sxwid/storyphone_attiny/Märchentelefon.kicad_sch

## KiCad design Märchentelefon.kicad_sch (2023-01-18)

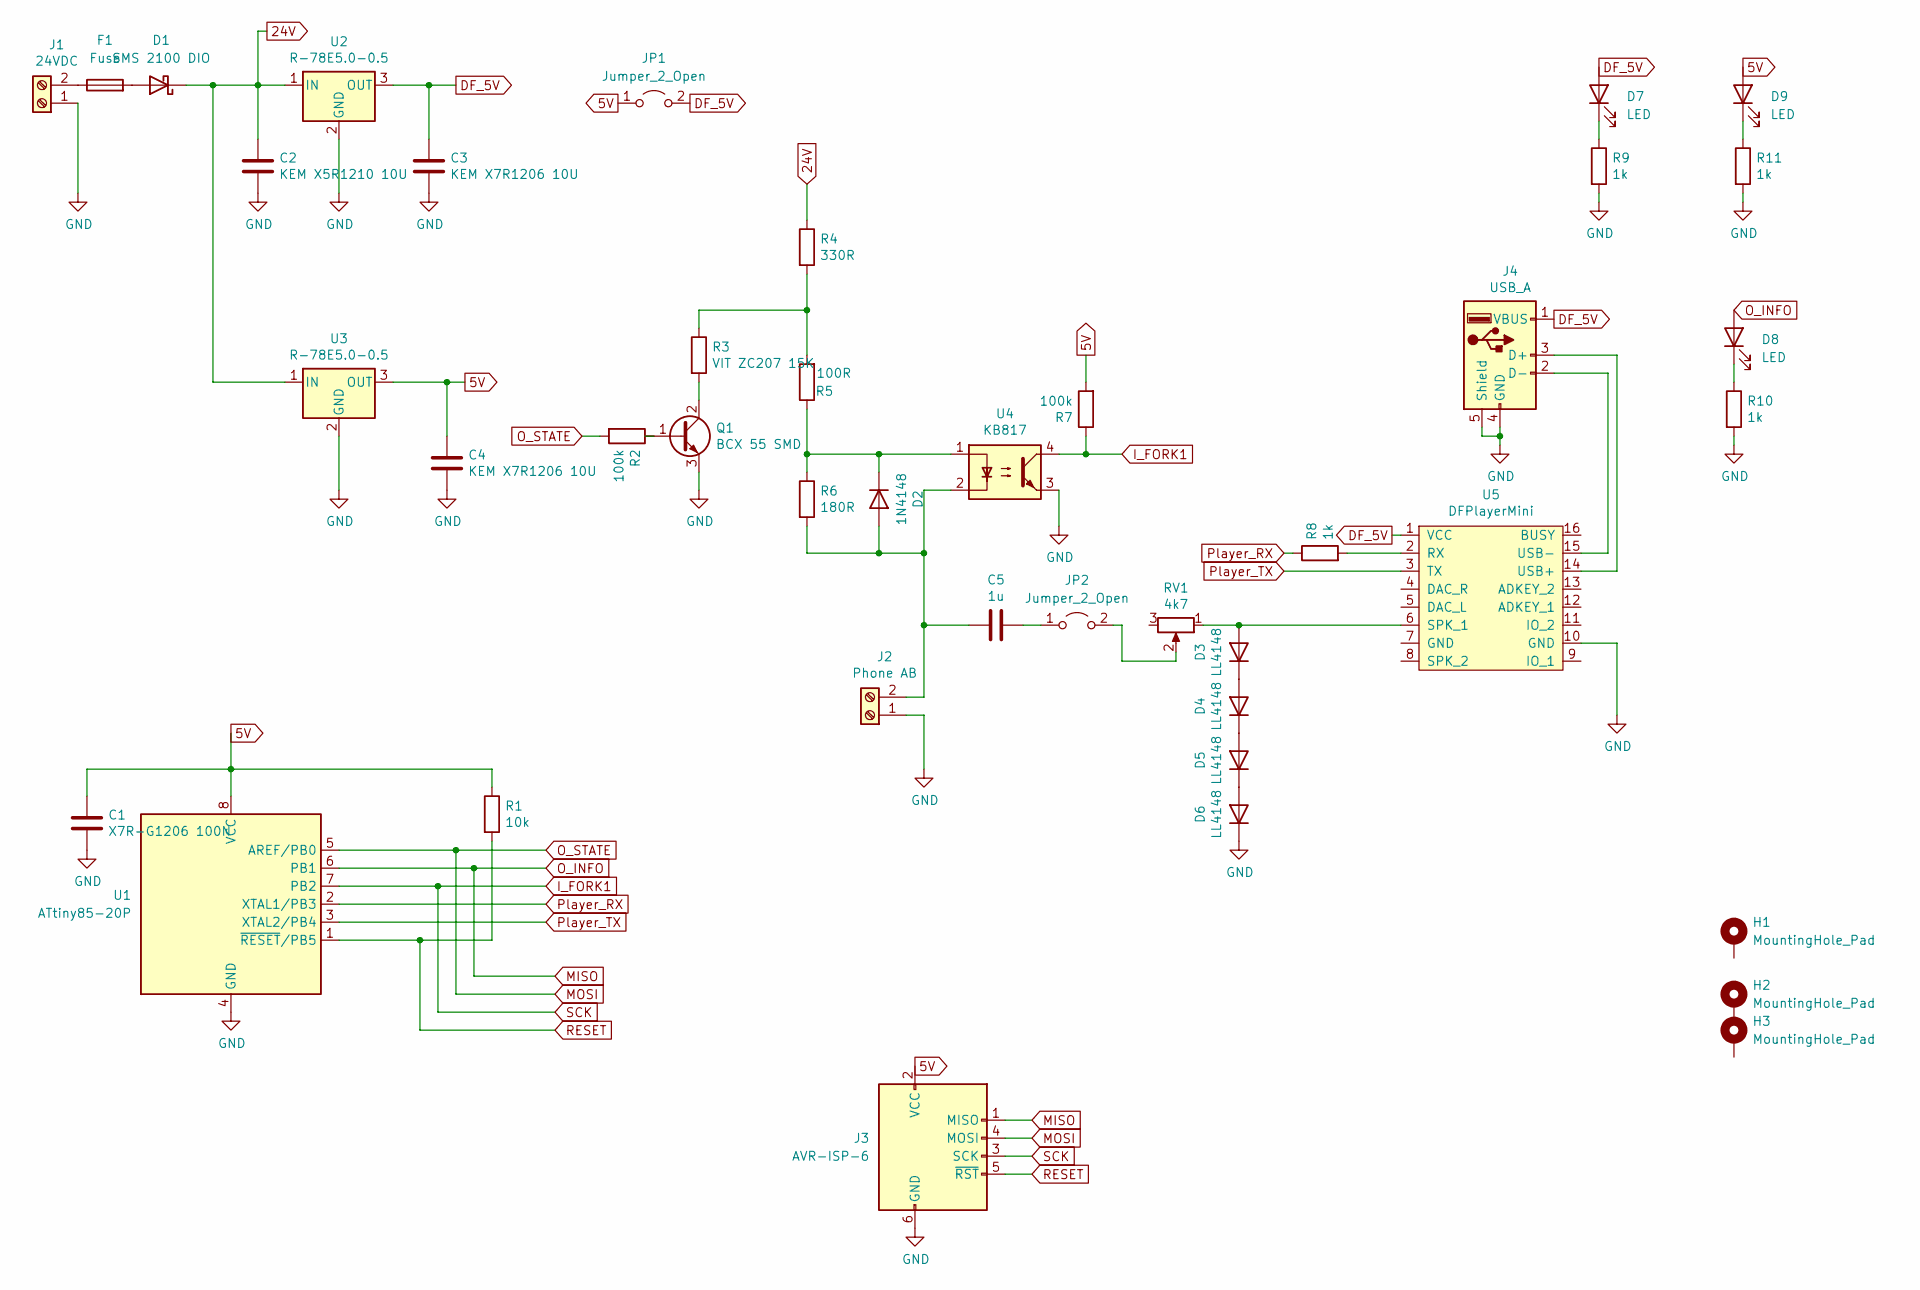
[picture p2: schematic Märchentelefon.kicad_sch]

Parts:
C1: X7R-G1206 100N; C_1206_3216Metric
C2: KEM X5R1210 10U; C_1210_3225Metric
C3, C4: KEM X7R1206 10U; C_1206_3216Metric
C5: 1u; C_Rect_L4.6mm_W5.5mm_P2.50mm_MKS02_FKP02
D1: SMS 2100 DIO; D_MELF_Handsoldering
D2: 1N4148; D_MiniMELF_Handsoldering
D3, D4, D5, D6: LL4148; D_MiniMELF_Handsoldering
D7, D8, D9: LED; LED_0805_2012Metric_Pad1.15x1.40mm_HandSolder
F1: Fuse; Fuse_2512_6332Metric_Pad1.52x3.35mm_HandSolder
H1, H2, H3: MountingHole_Pad; MountingHole_2.5mm
J1: 24VDC; PinSocket_1x02_P2.54mm_Vertical
J2: Phone AB; PinSocket_1x02_P2.54mm_Vertical
J3: AVR-ISP-6
J4: USB_A; USB_A_Molex_67643_Horizontal
JP1, JP2: Jumper_2_Open; L_0805_2012Metric_Pad1.15x1.40mm_HandSolder
Q1: BCX 55 SMD; SOT-89-3_Handsoldering
R1: 10k; R_0805_2012Metric_Pad1.20x1.40mm_HandSolder
R2, R7: 100k; R_0805_2012Metric_Pad1.20x1.40mm_HandSolder
R3: VIT ZC207 15K; R_MELF_MMB-0207
R4: 330R; R_0805_2012Metric_Pad1.20x1.40mm_HandSolder
R5: 100R; R_0805_2012Metric_Pad1.20x1.40mm_HandSolder
R6: 180R; R_0805_2012Metric_Pad1.20x1.40mm_HandSolder
R8, R9, R10, R11: 1k; R_0805_2012Metric_Pad1.20x1.40mm_HandSolder
RV1: 4k7; Potentiometer_Piher_T-16H_Single_Horizontal
U1: ATtiny85-20P; DIP-8_W7.62mm
U2, U3: R-78E5.0-0.5; Converter_DCDC_RECOM_R-78E-0.5_THT
U4: KB817; DIP-4_W7.62mm
U5: DFPlayerMini; DFPlayer_V2

Connections:
5V: C1.1, C4.1, D9.2 (A), J3.2 (VCC), JP1.1 (A), R1.1, R7.2, U1.8 (VCC), U3.3 (OUT)
24V: C2.1, D1.1 (K), R4.1, U2.1 (IN), U3.1 (IN)
DF_5V: C3.1, D7.2 (A), J4.1 (VBUS), JP1.2 (B), U2.3 (OUT), U5.1 (VCC)
GND: C1.2, C2.2, C3.2, C4.2, D6.1 (K), J1.1, J2.1, J3.6 (GND), J4.4 (GND), J4.5 (Shield), Q1.3 (E), R9.2, R10.2, R11.2, U1.4 (GND), U2.2 (GND), U3.2 (GND), U4.3, U5.10 (GND)
I_FORK1: J3.3 (SCK), R7.1, U1.7 (PB2), U4.4
MISO: D8.2 (A), J3.1 (MISO), U1.6 (PB1)
MOSI: J3.4 (MOSI), R2.2, U1.5 (AREF/PB0)
unnamed: C5.1, JP2.1 (A)
unnamed: C5.2, D2.2 (A), J2.2, R6.2, U4.2
unnamed: D1.2 (A), F1.2
unnamed: D2.1 (K), R5.1, R6.1, U4.1
unnamed: D3.1 (K), D4.2 (A)
unnamed: D3.2 (A), RV1.1, U5.6 (SPK_1)
unnamed: D4.1 (K), D5.2 (A)
unnamed: D5.1 (K), D6.2 (A)
unnamed: D7.1 (K), R9.1
unnamed: D8.1 (K), R10.1
unnamed: D9.1 (K), R11.1
unnamed: F1.1, J1.2
unnamed: J4.2 (D-), U5.15 (USB-)
unnamed: J4.3 (D+), U5.14 (USB+)
unnamed: JP2.2 (B), RV1.2
unnamed: Q1.1 (B), R2.1
unnamed: Q1.2 (C), R3.2
unnamed: R3.1, R4.2, R5.2
unnamed: R8.2, U5.2 (RX)
Player_RX: R8.1, U1.2 (XTAL1/PB3)
Player_TX: U1.3 (XTAL2/PB4), U5.3 (TX)
RESET: J3.5 (~RST), R1.2, U1.1 (~RESET/PB5)
